jwalthour/msld/mlb/utils.py

from rgbmatrix import RGBMatrixOptions, graphics
import collections
import argparse
import os
import debug

def get_file(path):
  dir = os.path.dirname(__file__)
  return os.path.join(dir, path)

def get_font():
  font = graphics.Font()
  font.LoadFont(get_file('Assets/4x6.bdf'))
  return font

def center_text_position(text, center_pos, font_width):
  return abs(center_pos - ((len(text) * font_width) / 2))

def split_string(string, num_chars):
  return [(string[i:i + num_chars]).strip() for i in range(0, len(string), num_chars)]

def args():
  parser = argparse.ArgumentParser()

  # Options for the rpi-rgb-led-matrix library
  parser.add_argument("--led-rows", action="store", help="Display rows. 16 for 16x32, 32 for 32x32. (Default: 32)", default=32, type=int)
  parser.add_argument("--led-cols", action="store", help="Panel columns. Typically 32 or 64. (Default: 32)", default=32, type=int)
  parser.add_argument("--led-chain", action="store", help="Daisy-chained boards. (Default: 1)", default=1, type=int)
  parser.add_argument("--led-parallel", action="store", help="For Plus-models or RPi2: parallel chains. 1..3. (Default: 1)", default=1, type=int)
  parser.add_argument("--led-pwm-bits", action="store", help="Bits used for PWM. Range 1..11. (Default: 11)", default=11, type=int)
  parser.add_argument("--led-brightness", action="store", help="Sets brightness level. Range: 1..100. (Default: 100)", default=100, type=int)
  parser.add_argument("--led-gpio-mapping", help="Hardware Mapping: regular, adafruit-hat, adafruit-hat-pwm" , choices=['regular', 'adafruit-hat', 'adafruit-hat-pwm'], type=str)
  parser.add_argument("--led-scan-mode", action="store", help="Progressive or interlaced scan. 0 = Progressive, 1 = Interlaced. (Default: 1)", default=1, choices=list(range(2)), type=int)
  parser.add_argument("--led-pwm-lsb-nanoseconds", action="store", help="Base time-unit for the on-time in the lowest significant bit in nanoseconds. (Default: 130)", default=130, type=int)
  parser.add_argument("--led-show-refresh", action="store_true", help="Shows the current refresh rate of the LED panel.")
  parser.add_argument("--led-slowdown-gpio", action="store", help="Slow down writing to GPIO. Range: 0..4. (Default: 1)", choices=list(range(5)), type=int)
  parser.add_argument("--led-no-hardware-pulse", action="store", help="Don't use hardware pin-pulse generation.")
  parser.add_argument("--led-rgb-sequence", action="store", help="Switch if your matrix has led colors swapped. (Default: RGB)", default="RGB", type=str)
  parser.add_argument("--led-pixel-mapper", action="store", help="Apply pixel mappers. e.g \"Rotate:90\"", default="", type=str)
  parser.add_argument("--led-row-addr-type", action="store", help="0 = default; 1 = AB-addressed panels; 2 = direct row select; 3 = ABC-addressed panels. (Default: 0)", default=0, type=int, choices=[0, 1, 2, 3])
  parser.add_argument("--led-multiplexing", action="store",
                      help="Multiplexing type: 0 = direct; 1 = strip; 2 = checker; 3 = spiral; 4 = Z-strip; 5 = ZnMirrorZStripe; 6 = coreman; 7 = Kaler2Scan; 8 = ZStripeUneven. (Default: 0)", default=0, type=int)

  return parser.parse_args()

def led_matrix_options(args):
  options = RGBMatrixOptions()

  if args.led_gpio_mapping != None:
    options.hardware_mapping = args.led_gpio_mapping

  options.rows = args.led_rows
  options.cols = args.led_cols
  options.chain_length = args.led_chain
  options.parallel = args.led_parallel
  options.row_address_type = args.led_row_addr_type
  options.multiplexing = args.led_multiplexing
  options.pwm_bits = args.led_pwm_bits
  options.brightness = args.led_brightness
  options.pwm_lsb_nanoseconds = args.led_pwm_lsb_nanoseconds
  options.led_rgb_sequence = args.led_rgb_sequence
  try:
    options.pixel_mapper_config = args.led_pixel_mapper
  except AttributeError:
    debug.warning("Your compiled RGB Matrix Library is out of date.")
    debug.warning("The --led-pixel-mapper argument will not work until it is updated.")

  if args.led_show_refresh:
    options.show_refresh_rate = 1

  if args.led_slowdown_gpio != None:
    options.gpio_slowdown = args.led_slowdown_gpio

  if args.led_no_hardware_pulse:
    options.disable_hardware_pulsing = True

  return options


def deep_update(source, overrides):
    """Update a nested dictionary or similar mapping.
    Modify ``source`` in place.
    """
    for key, value in list(overrides.items()):
        if isinstance(value, collections.Mapping) and value:
            returned = deep_update(source.get(key, {}), value)
            source[key] = returned
        else:
            source[key] = overrides[key]
    return source
